SecSelS/SecSi-Energy-Monitor/Render/P1_shield_board_2.jpg

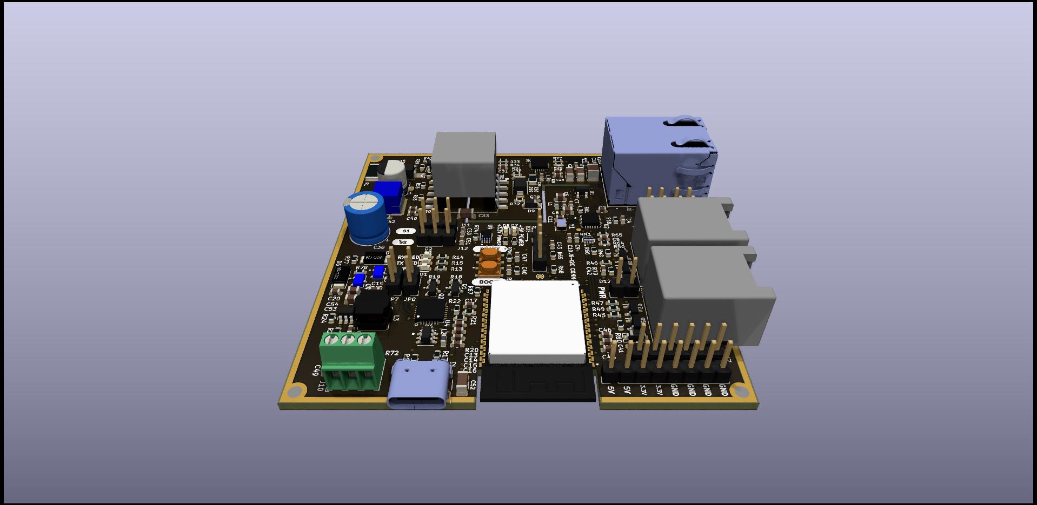
Render/P1_shield_board_2.jpg
