SecSelS/SecSi-Energy-Monitor/Render/P1_shield_board_3.jpg

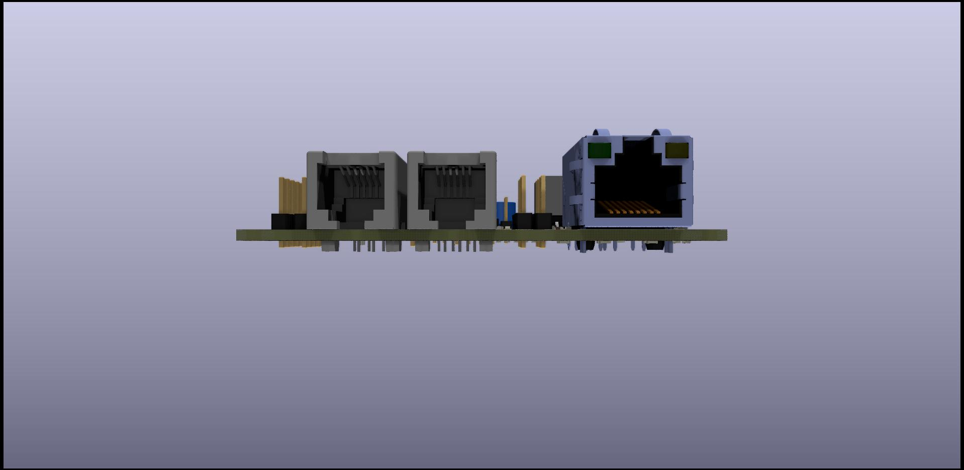
Render/P1_shield_board_3.jpg
